AlessioPasin/Progetto-di-tesi-LiDAR/Simulazioni_LTSpace/Simulazione_LT1719.asc

U1: LT1719
V1: voltage; 3.3
V2: voltage; PULSE(0 500m 0 1n 1n 1n 0 1)
Vs: voltage; 0.1
Named nets: 0, 3V3, OUT, Vin, Vs
.tran 10n
Vs = Tensione di soglia
