AlessioPasin/Progetto-di-tesi-LiDAR/Simulazioni_LTSpace/Simulazione_LT1719_condizionata.asc

C1: cap; 50p
D1: schottky; RB511VM-30
R2: res; 47
R3: res; 180
U1: LT1719
V1: voltage; 3.3
V2: voltage; PULSE(0 {Vmax} 0 1n 1n 1n 0 1)
Vs: voltage; 0.1
Named nets: 0, 3V3, OUT, Vsig, Vin, Vs
.tran 50n
Vs = Tensione di soglia
.step param Vmax 500m 2 500m
.lib opamp.sub
